Ryz3D/HERA/compiler/src/includes.h

#pragma once

#include <malloc.h>
#include <stdbool.h>
#include <stdint.h>
#include <stdio.h>
#include <string.h>

#define DEBUG 1
#define DEBUG_SRC "./programs/c/test.c"
#define ENDL "\r\n"
#define FILE_ENDL "\n"
#define ASM_INDENT "    "
#define ERROR "\e[1;5;31mERROR:\e[m "
#define OK "\e[1;96mok\e[m"
#define NOK "\e[1;33mno way\e[m"

#include "tokenizer.c"
#include "preprocessor.c"
#include "parser.c"
#include "asm.c"
